galsabag8/IOT_REPO_Group4/ESP32/IMU_with_Madgwick/MadgwickAlgo.h

#ifndef MADGWICK_ALGO_H
#define MADGWICK_ALGO_H

#include <Arduino.h>
#include "config.h"

// Expose variables needed by main (for screen mapping)
extern float q0, q1, q2, q3; 

void MadgwickUpdate(float gx, float gy, float gz, float ax, float ay, float az, float dt);

#endif
